Parconier/OTUS/Construction System/Enclosures - v0.2/Actuators/Motor - v0.1/motor_closure1p_color_x2_v0.1.stl

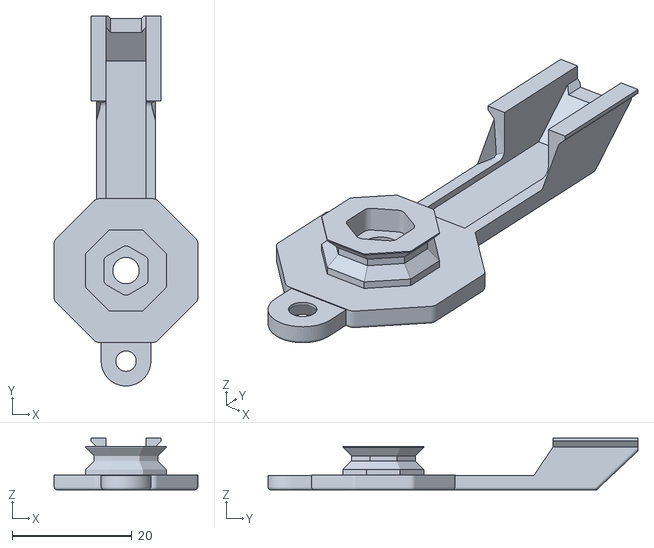
[picture p18: CAD file, 2019-10-22]
Construction System/Enclosures - v0.2/Actuators/Motor - v0.1/motor_closure1p_color_x2_v0.1.stl
24.0 x 61.8 x 8.65
