Parconier/OTUS/Construction System/Enclosures - v0.2/Actuators/Potenciometer - v0.2/pote_knob_neutral_x1_v0.2.stl

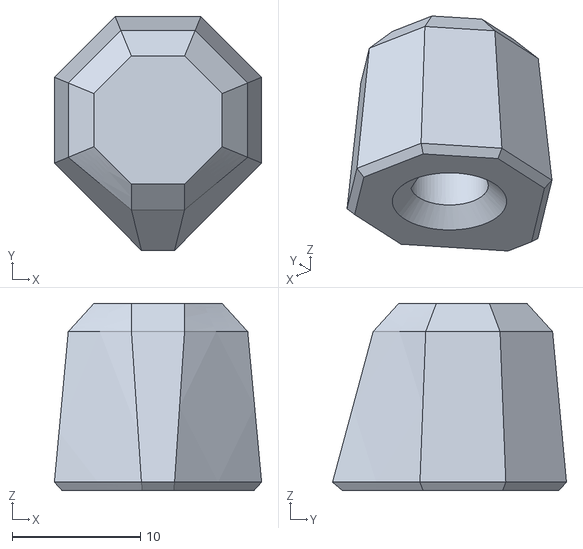
[picture p19: CAD file, 2019-10-22]
Construction System/Enclosures - v0.2/Actuators/Potenciometer - v0.2/pote_knob_neutral_x1_v0.2.stl
16.2 x 18.3 x 14.6
