Parconier/OTUS/Construction System/Enclosures - v0.2/Actuators/Servomotor - v0.1/servo_closure_neutral_x2_v0.1.stl

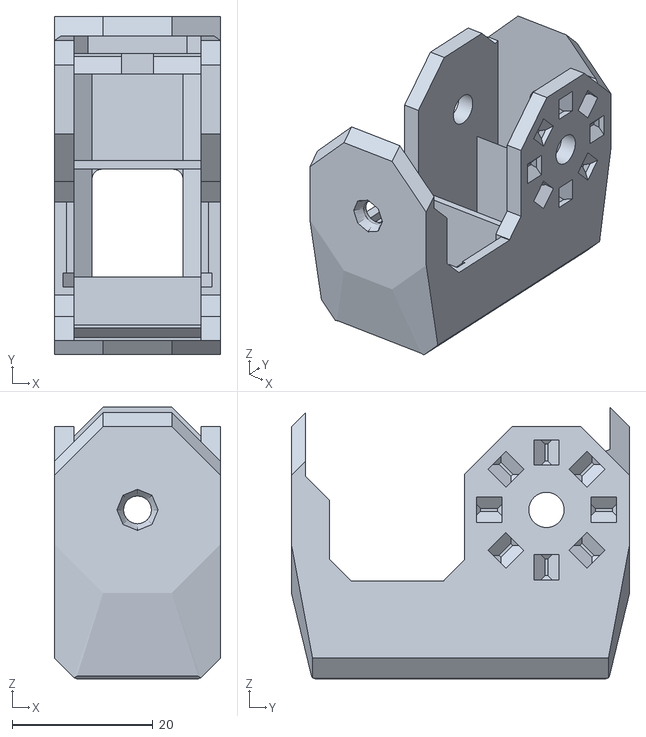
[picture p20: CAD file, 2019-10-22]
Construction System/Enclosures - v0.2/Actuators/Servomotor - v0.1/servo_closure_neutral_x2_v0.1.stl
23.6 x 48.0 x 38.6
