Parconier/OTUS/Construction System/Enclosures - v0.2/Others/Adapter - v0.2/adapter_male_color_x1_v0.2.stl

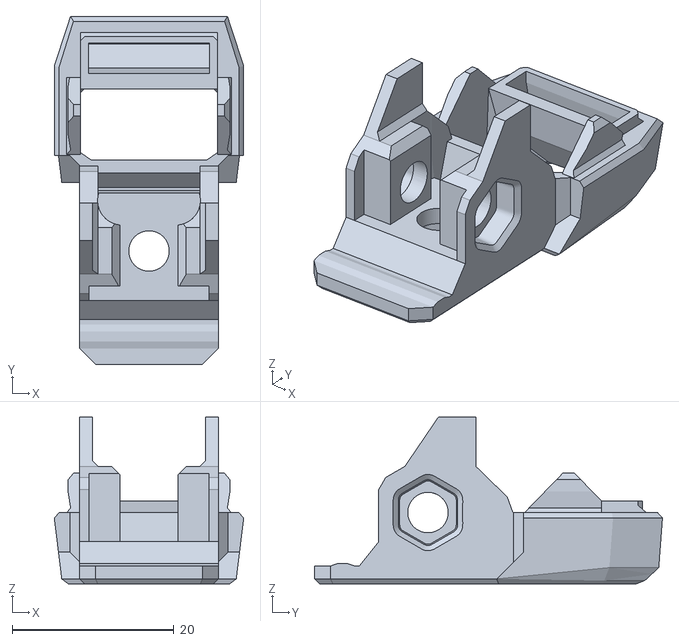
[picture p22: CAD file, 2019-10-22]
Construction System/Enclosures - v0.2/Others/Adapter - v0.2/adapter_male_color_x1_v0.2.stl
23.4 x 43.1 x 20.6
