Parconier/OTUS/Construction System/Enclosures - v0.2/Sensors/Contrast_Sensor - v0.2/contrast_female_color_x2_v0.2.stl

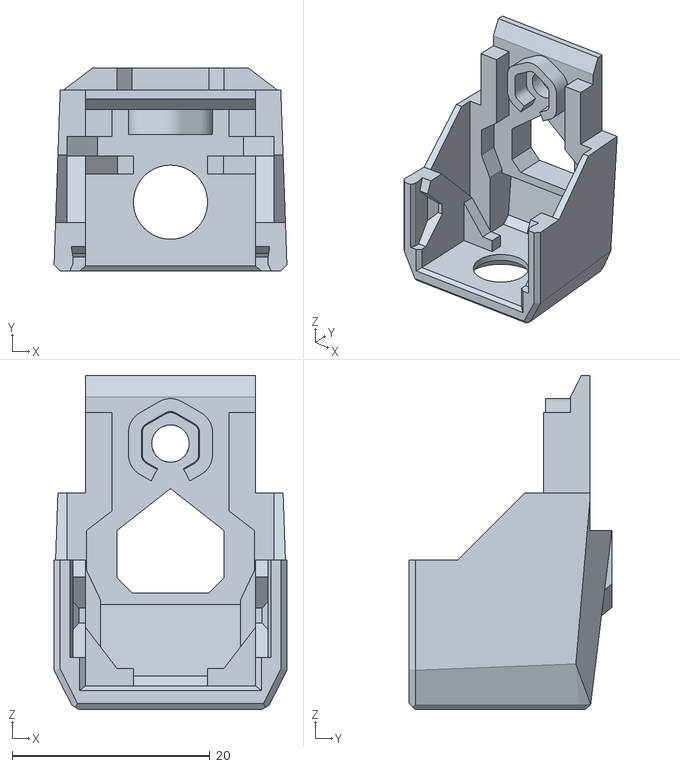
[picture p24: CAD file, 2019-10-22]
Construction System/Enclosures - v0.2/Sensors/Contrast_Sensor - v0.2/contrast_female_color_x2_v0.2.stl
23.6 x 20.5 x 33.8
