Parconier/OTUS/Construction System/Enclosures - v0.2/Sensors/Distance_Sensor - v0.2/distance_male_neutral_x1_v0.2.stl

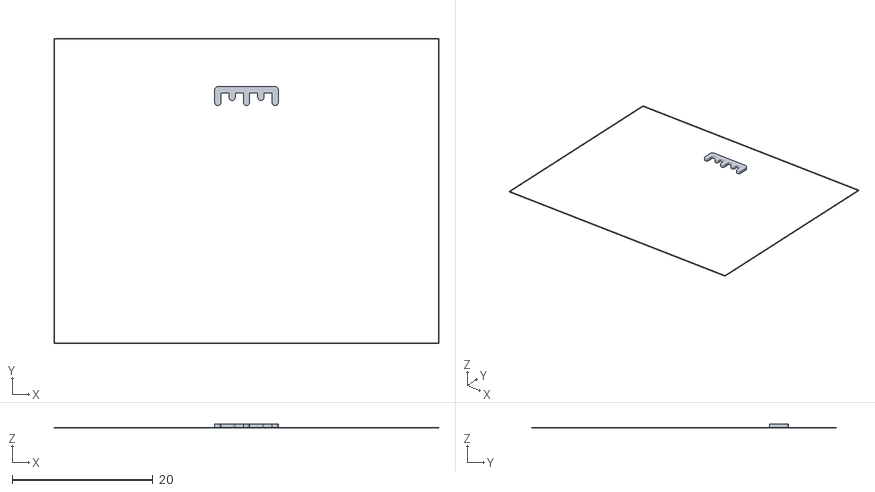
[picture p25: CAD file, 2019-10-22]
Construction System/Enclosures - v0.2/Sensors/Distance_Sensor - v0.2/distance_male_neutral_x1_v0.2.stl
54.6 x 43.4 x 0.6
