Parconier/OTUS/Construction System/Enclosures - v0.2/Sensors/LED_Matrix_3x3 - v0.2/LEDM3x3_male_color_x1_v0.2.stl

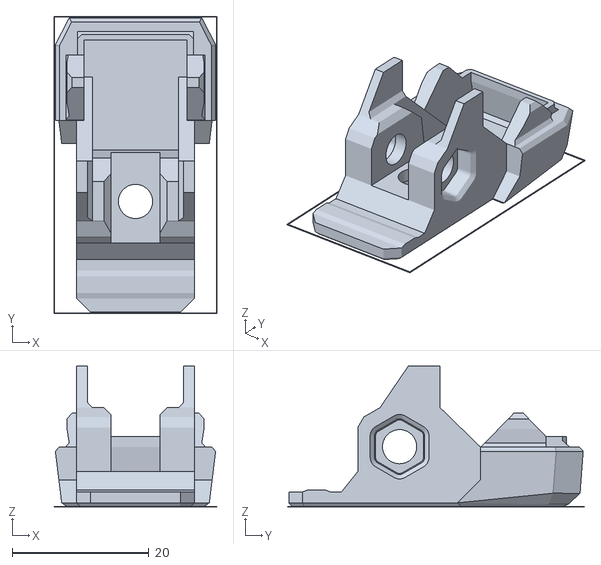
[picture p27: CAD file, 2019-10-22]
Construction System/Enclosures - v0.2/Sensors/LED_Matrix_3x3 - v0.2/LEDM3x3_male_color_x1_v0.2.stl
23.8 x 43.5 x 20.6
