Parconier/OTUS/Construction System/Others - v0.2/Omni_wheel - v0.2/Omni_wheel_color_x1_v0.2.stl

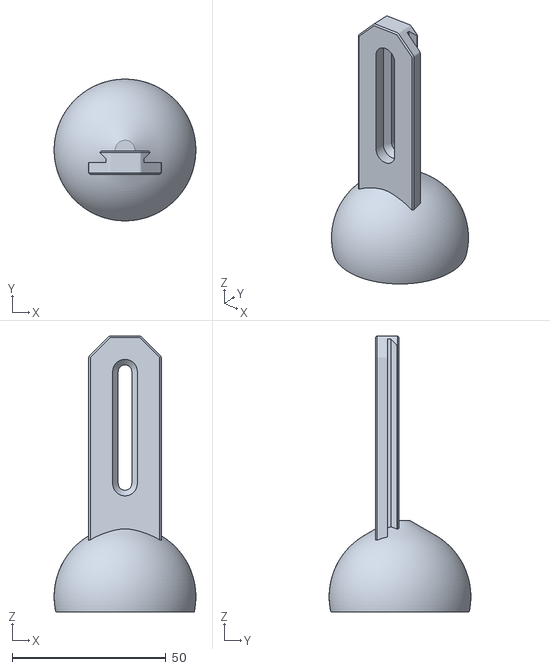
[picture p28: CAD file, 2019-10-22]
Construction System/Others - v0.2/Omni_wheel - v0.2/Omni_wheel_color_x1_v0.2.stl
46.1 x 46.1 x 89.8
