Parconier/OTUS/Construction System/Patterns - v0.2/90degrees_color_x4 - v0.2.stl

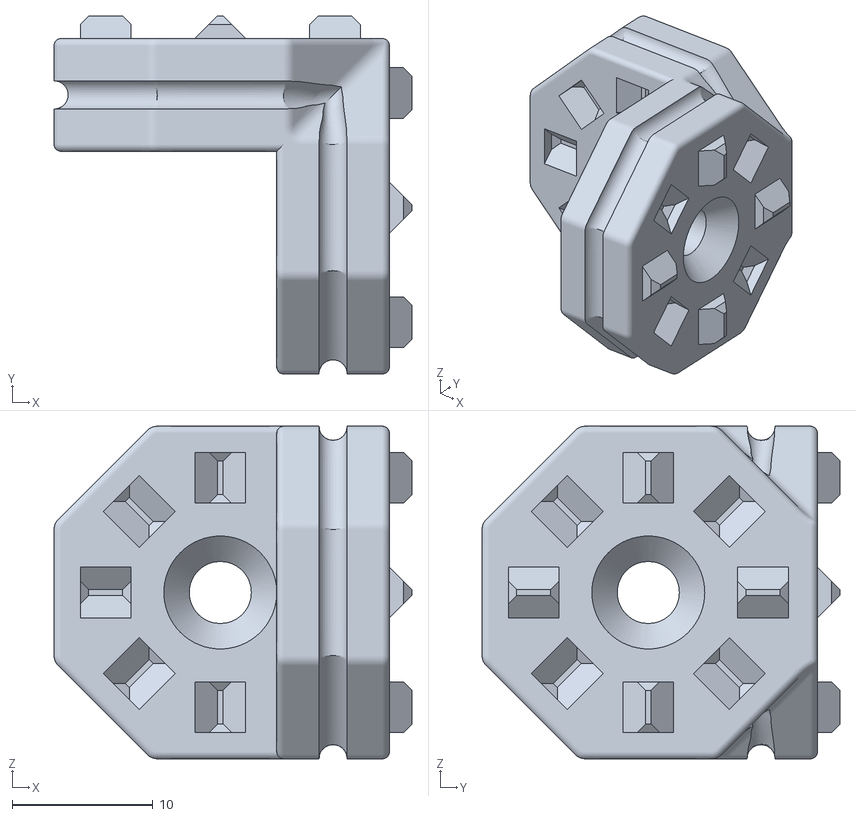
[picture p29: CAD file, 2019-10-18]
Construction System/Patterns - v0.2/90degrees_color_x4 - v0.2.stl
25.4 x 25.4 x 23.6
