Parconier/OTUS/Construction System/Enclosures - v0.2/Actuators/Motor - v0.1/wheel_color_x2_v0.1.stl

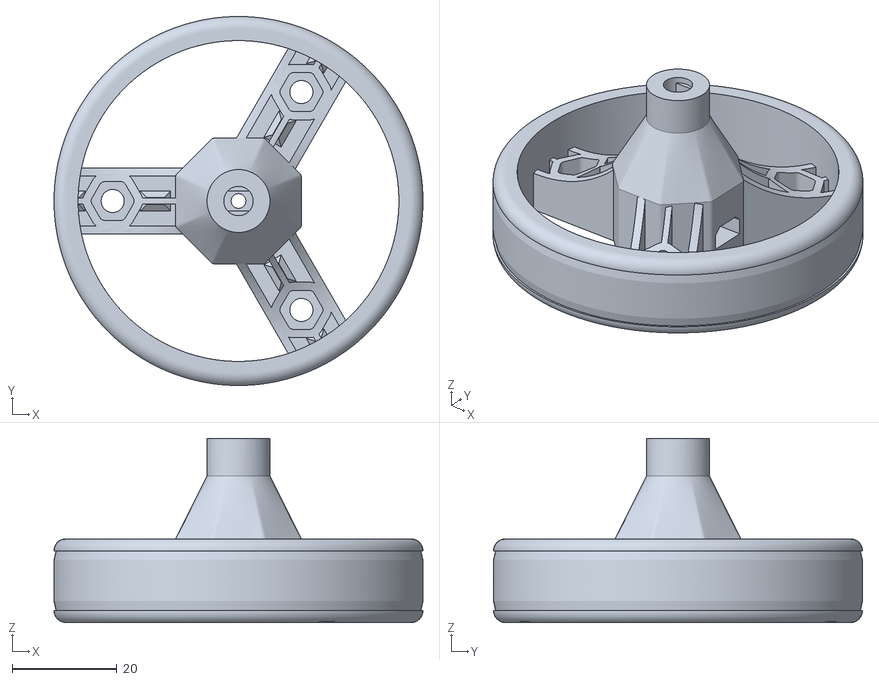
[picture p30: CAD file, 2019-10-22]
Construction System/Enclosures - v0.2/Actuators/Motor - v0.1/wheel_color_x2_v0.1.stl
70.4 x 70.4 x 35.2
