Parconier/OTUS/Construction System/Enclosures - v0.2/Actuators/Potenciometer - v0.2/pote_closure_neutral_x1_v0.2.stl

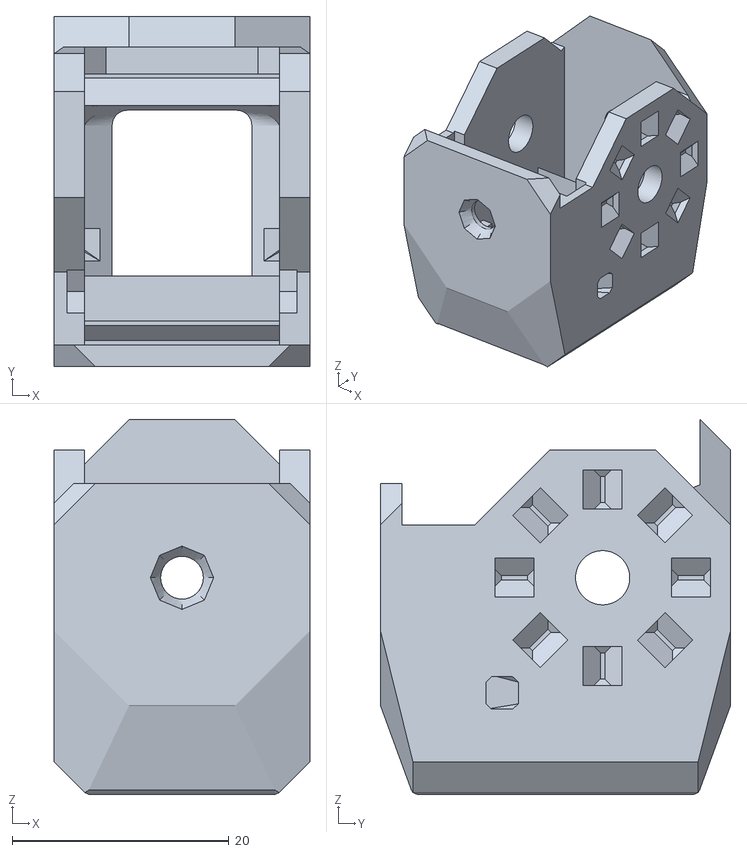
[picture p31: CAD file, 2019-10-22]
Construction System/Enclosures - v0.2/Actuators/Potenciometer - v0.2/pote_closure_neutral_x1_v0.2.stl
23.6 x 32.3 x 34.6
