Parconier/OTUS/Construction System/Enclosures - v0.2/Interface - v0.2/interface_motor_color_x1_v0.2.stl

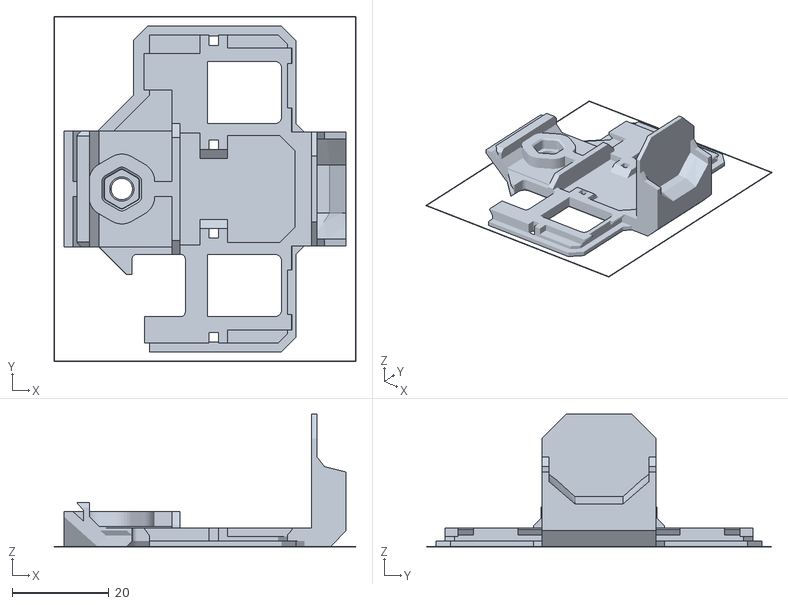
[picture p33: CAD file, 2019-10-22]
Construction System/Enclosures - v0.2/Interface - v0.2/interface_motor_color_x1_v0.2.stl
62.4 x 71.3 x 27.4
