Parconier/OTUS/Construction System/Enclosures - v0.2/Others/Adapter - v0.2/adapter_closure_neutral_x1_v0.2.stl

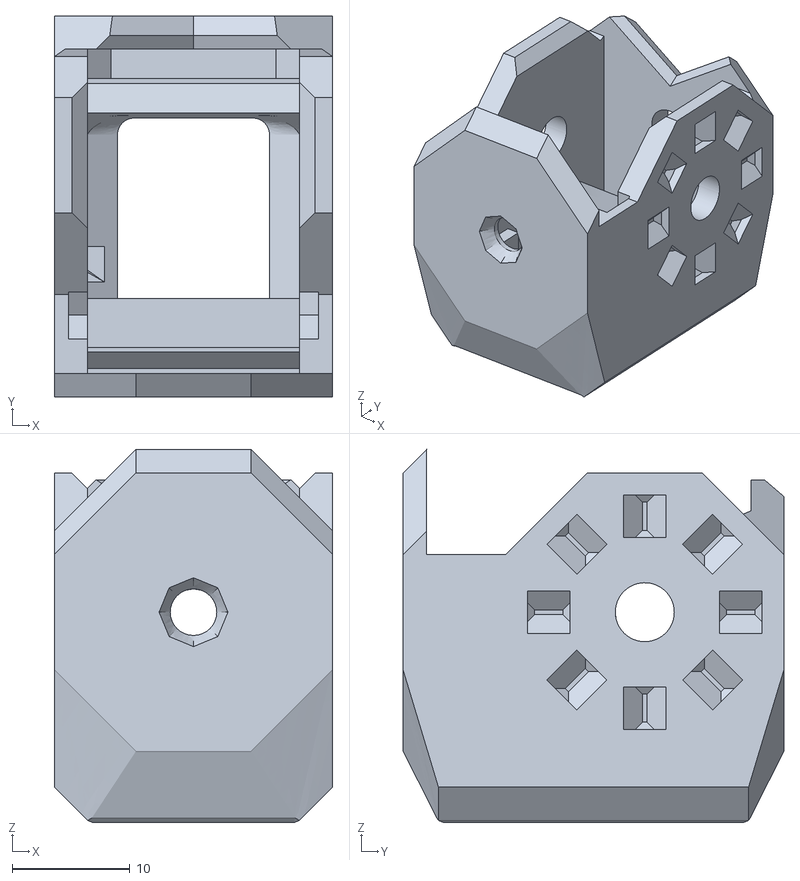
[picture p34: CAD file, 2019-10-22]
Construction System/Enclosures - v0.2/Others/Adapter - v0.2/adapter_closure_neutral_x1_v0.2.stl
23.6 x 32.3 x 31.6
