Parconier/OTUS/Construction System/Enclosures - v0.2/Sensors/Button_Sensor - v0.2/button_button_neutral_x1_v0.2.stl

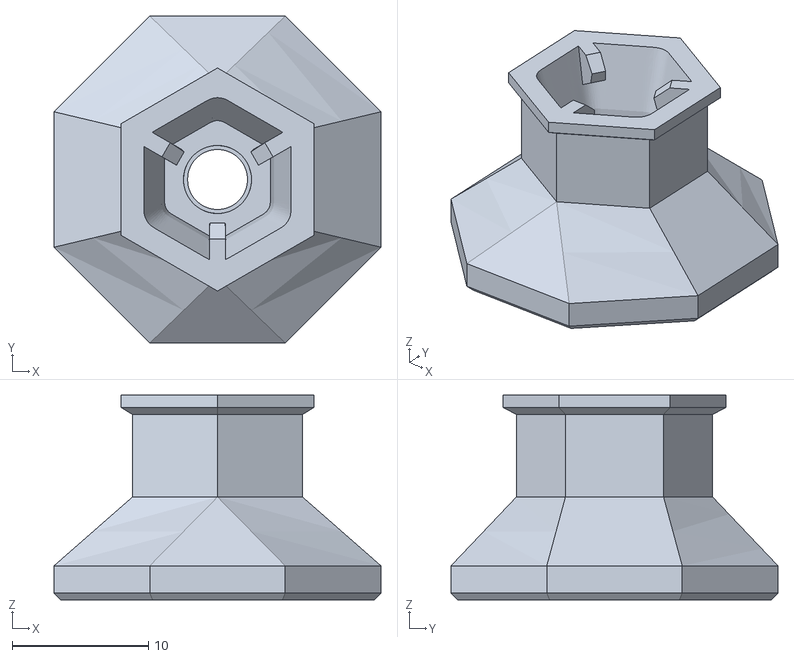
[picture p35: CAD file, 2019-10-22]
Construction System/Enclosures - v0.2/Sensors/Button_Sensor - v0.2/button_button_neutral_x1_v0.2.stl
24.0 x 24.0 x 15.0
