Parconier/OTUS/Construction System/Enclosures - v0.2/Sensors/Contrast_Sensor - v0.2/contrast_male_neutral_x2_v0.2.stl

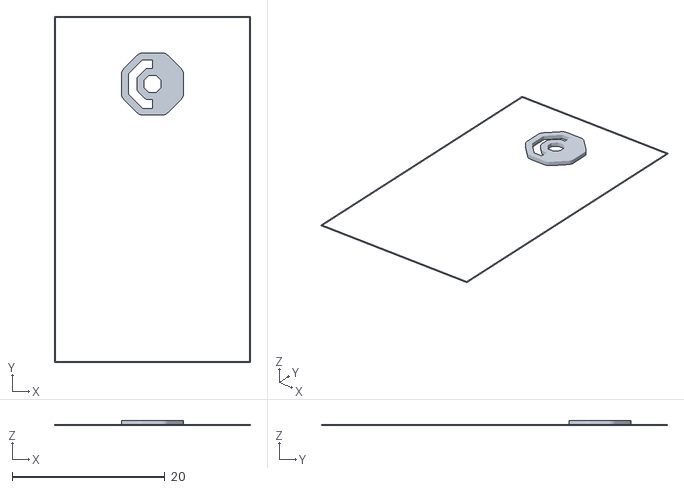
[picture p36: CAD file, 2019-10-22]
Construction System/Enclosures - v0.2/Sensors/Contrast_Sensor - v0.2/contrast_male_neutral_x2_v0.2.stl
25.6 x 45.3 x 0.6
