Parconier/OTUS/Construction System/Enclosures - v0.2/Sensors/LED_Matrix_3x3 - v0.2/LEDM3x3_female_color_x1_v0.2.stl

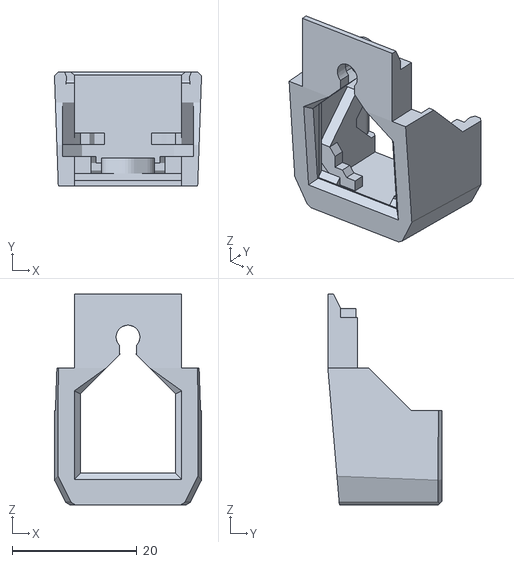
[picture p39: CAD file, 2019-10-22]
Construction System/Enclosures - v0.2/Sensors/LED_Matrix_3x3 - v0.2/LEDM3x3_female_color_x1_v0.2.stl
23.6 x 18.3 x 33.8
