Parconier/OTUS/Construction System/Others - v0.2/Omni_wheel - v0.2/Omni_wheel_v0.2.stp

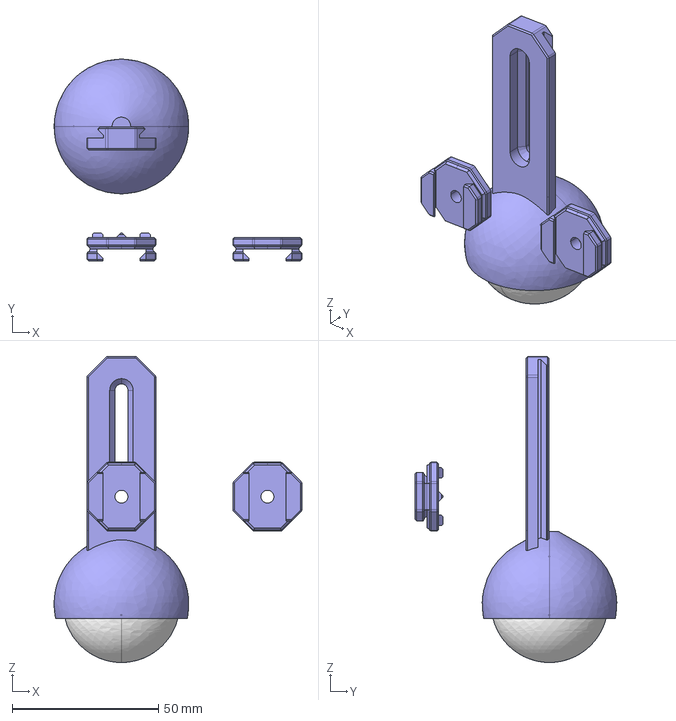
[picture p40: CAD file, 2019-10-22]
Construction System/Others - v0.2/Omni_wheel - v0.2/Omni_wheel_v0.2.stp
84.9 x 69.1 x 104.8 mm
