Parconier/OTUS/Construction System/Patterns - v0.2/Patternx2_color_x6 - v0.2.stl

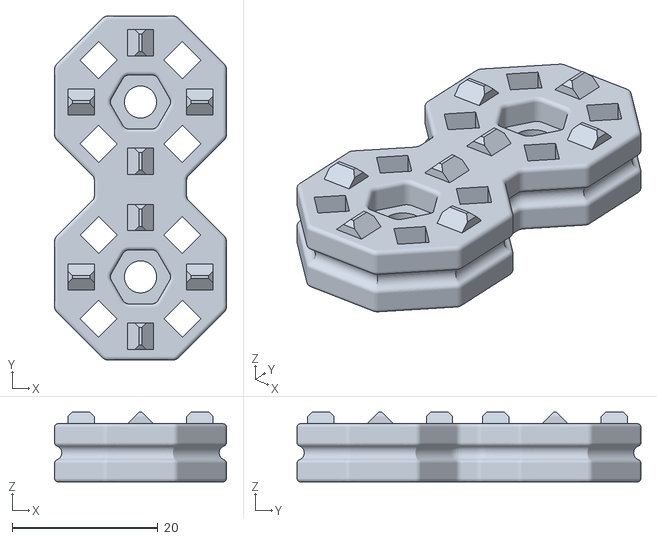
[picture p41: CAD file, 2019-10-18]
Construction System/Patterns - v0.2/Patternx2_color_x6 - v0.2.stl
23.6 x 47.2 x 9.60
