Parconier/OTUS/Construction System/Enclosures - v0.2/Actuators/Motor - v0.1/motor_male_neutral_x2_v0.1.stl

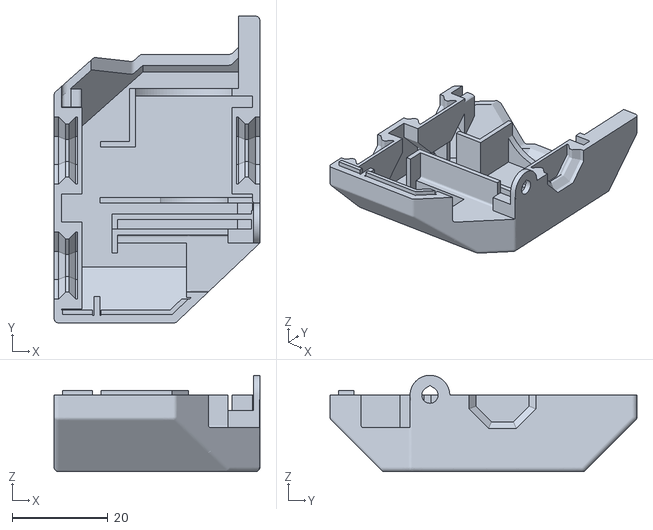
[picture p42: CAD file, 2019-10-22]
Construction System/Enclosures - v0.2/Actuators/Motor - v0.1/motor_male_neutral_x2_v0.1.stl
43.0 x 64.1 x 20.1
