Parconier/OTUS/Construction System/Enclosures - v0.2/Actuators/Servomotor - v0.1/servo_male_color_x2_v0.1.stl

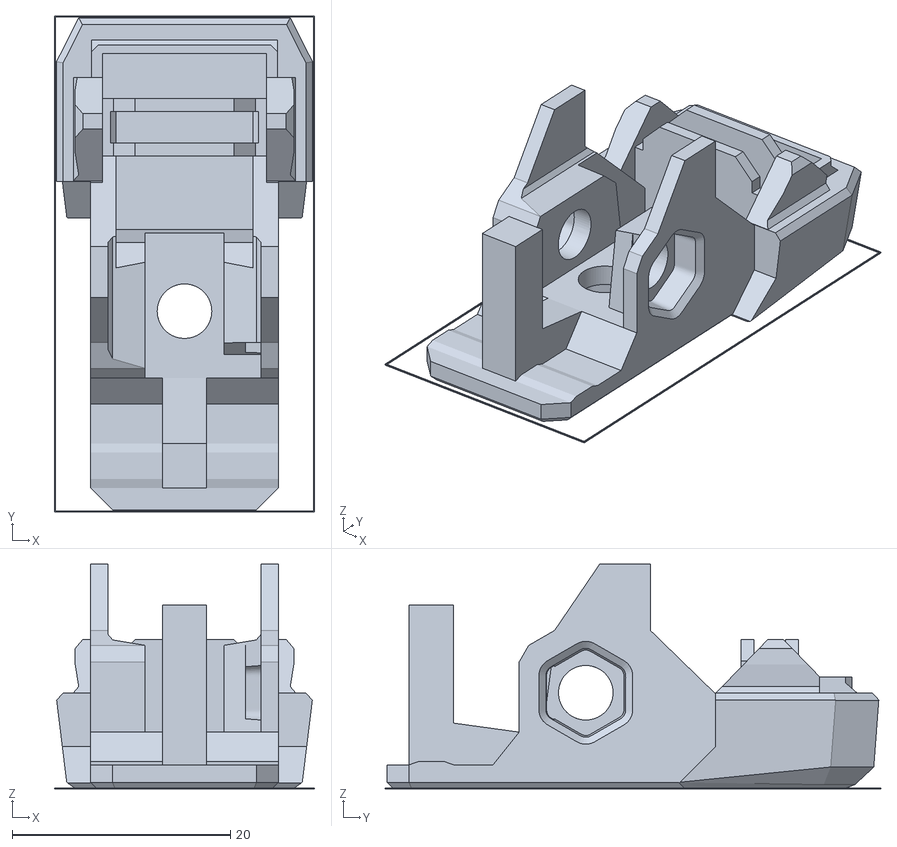
[picture p43: CAD file, 2019-10-22]
Construction System/Enclosures - v0.2/Actuators/Servomotor - v0.1/servo_male_color_x2_v0.1.stl
23.8 x 45.5 x 20.6
