Parconier/OTUS/Construction System/Enclosures - v0.2/Interface - v0.2/interface_sideA_neutral_x1_v0.2.stl

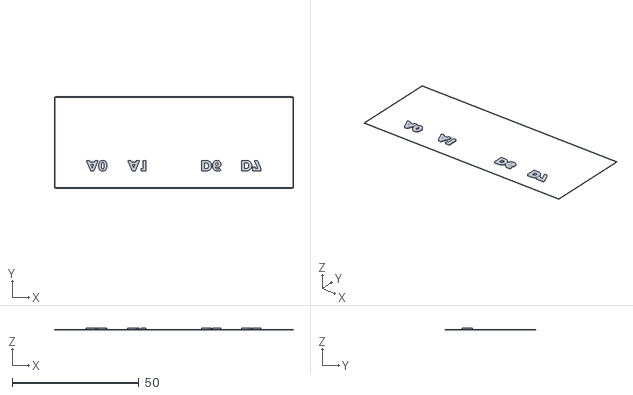
[picture p44: CAD file, 2019-10-22]
Construction System/Enclosures - v0.2/Interface - v0.2/interface_sideA_neutral_x1_v0.2.stl
94.2 x 36.0 x 0.6
