Parconier/OTUS/Construction System/Enclosures - v0.2/Others/Adapter - v0.2/adapter_female_color_x1_v0.2.stl

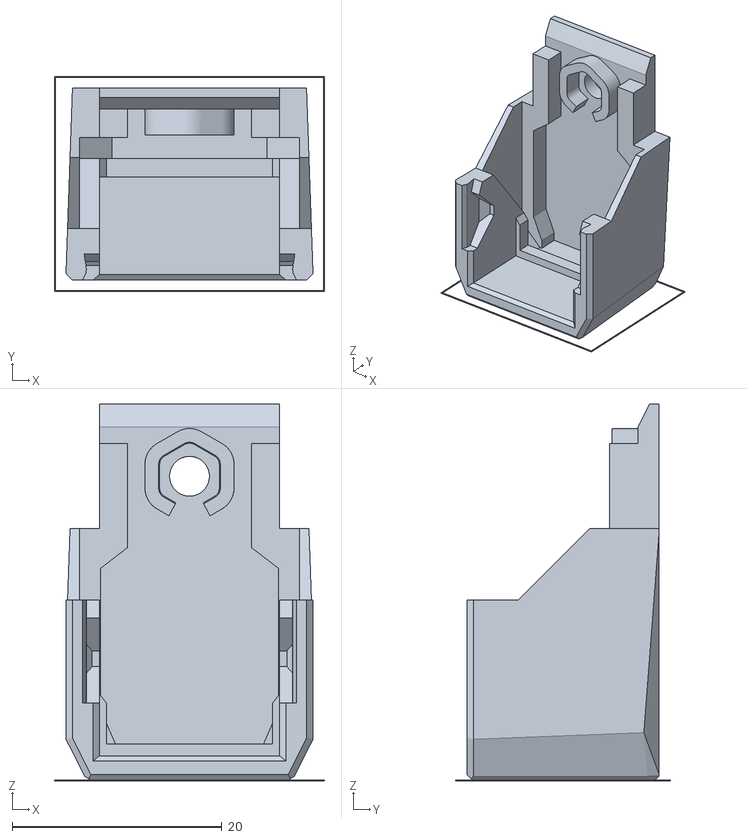
[picture p45: CAD file, 2019-10-22]
Construction System/Enclosures - v0.2/Others/Adapter - v0.2/adapter_female_color_x1_v0.2.stl
25.8 x 20.5 x 35.9
