Parconier/OTUS/Construction System/Enclosures - v0.2/Sensors/Button_Sensor - v0.2/button_female_color_x1_v0.2.stl

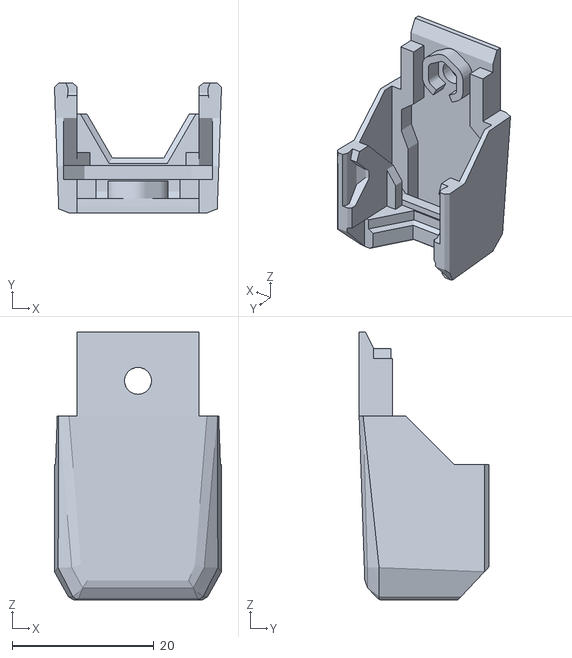
[picture p46: CAD file, 2019-10-22]
Construction System/Enclosures - v0.2/Sensors/Button_Sensor - v0.2/button_female_color_x1_v0.2.stl
23.6 x 18.3 x 37.8
