Parconier/OTUS/Construction System/Enclosures - v0.2/Sensors/Distance_Sensor - v0.2/distance_female_color_x1_v0.2.stl

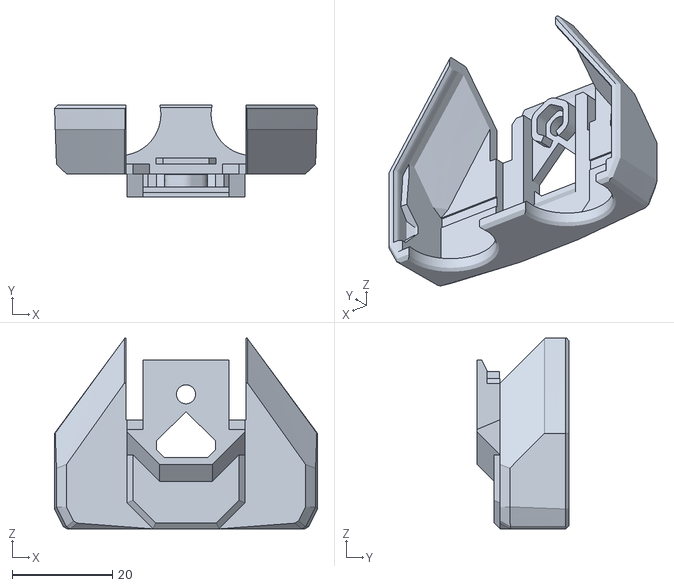
[picture p47: CAD file, 2019-10-22]
Construction System/Enclosures - v0.2/Sensors/Distance_Sensor - v0.2/distance_female_color_x1_v0.2.stl
52.6 x 18.3 x 38.1
