Parconier/OTUS/Construction System/Enclosures - v0.2/Sensors/LED_Matrix_3x3 - v0.2/LEDM3x3_closure_neutral_x1_v0.2.stl

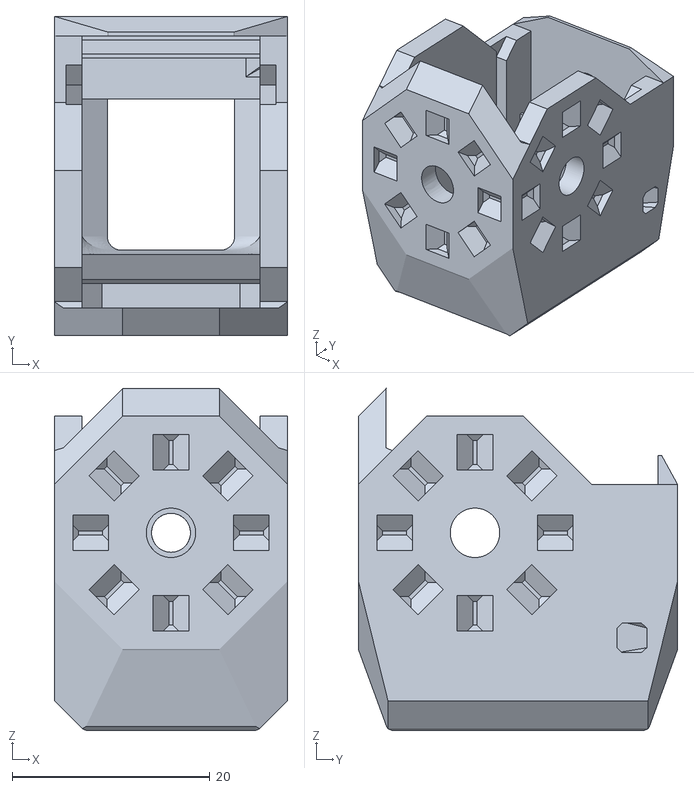
[picture p48: CAD file, 2019-10-22]
Construction System/Enclosures - v0.2/Sensors/LED_Matrix_3x3 - v0.2/LEDM3x3_closure_neutral_x1_v0.2.stl
23.6 x 32.3 x 34.6
