Parconier/OTUS/Construction System/Patterns - v0.2/Patternx3_color_x2 - v0.2.stl

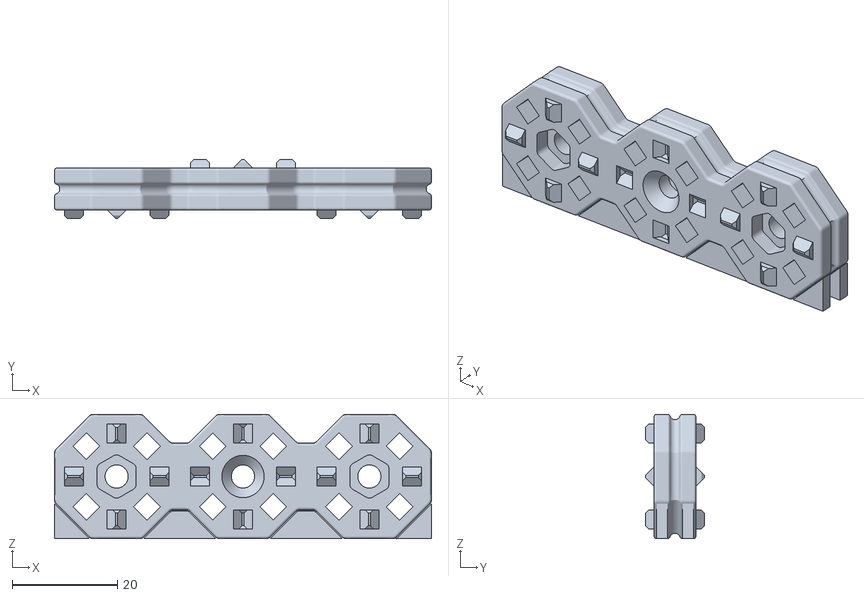
[picture p49: CAD file, 2019-10-18]
Construction System/Patterns - v0.2/Patternx3_color_x2 - v0.2.stl
71.6 x 11.2 x 23.6
