Parconier/OTUS/Construction System/Enclosures - v0.2/Actuators/Potenciometer - v0.2/pote_male_neutral_x1_v0.2.stl

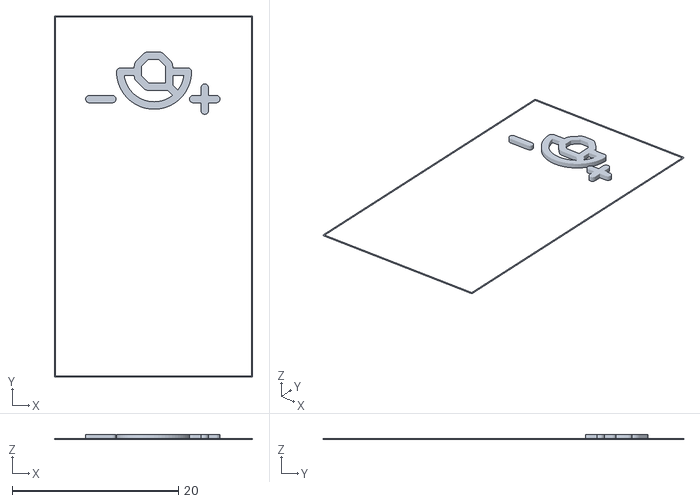
[picture p51: CAD file, 2019-10-22]
Construction System/Enclosures - v0.2/Actuators/Potenciometer - v0.2/pote_male_neutral_x1_v0.2.stl
23.8 x 43.5 x 0.6
