Parconier/OTUS/Construction System/Enclosures - v0.2/Sensors/Button_Sensor - v0.2/button_male_neutral_x1_v0.2.stl

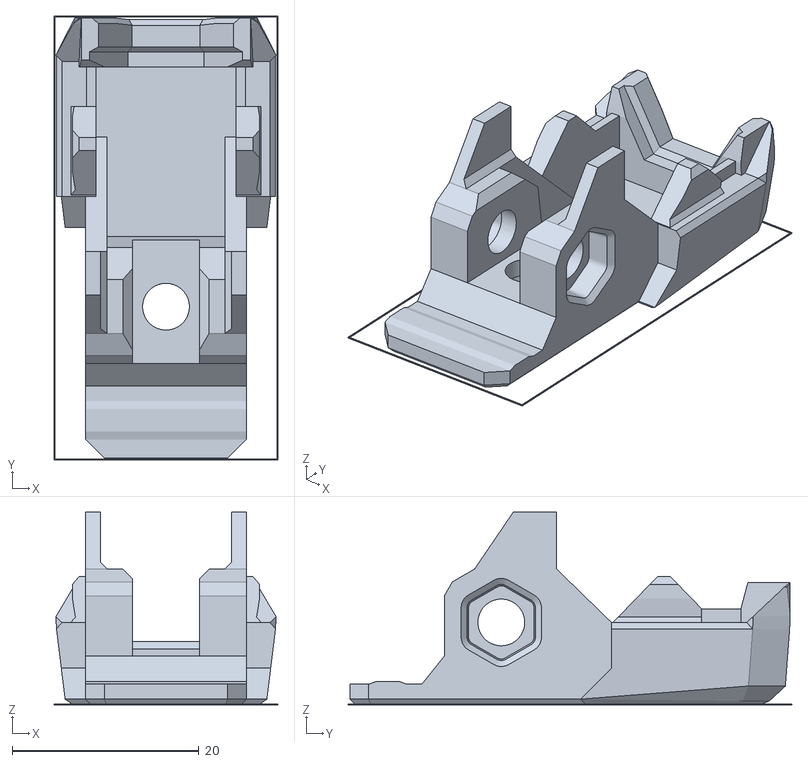
[picture p54: CAD file, 2019-10-22]
Construction System/Enclosures - v0.2/Sensors/Button_Sensor - v0.2/button_male_neutral_x1_v0.2.stl
24.0 x 47.5 x 20.6
