Parconier/OTUS/Construction System/Enclosures - v0.2/Actuators/Motor - v0.1/motor_female_neutral_x2_v0.1.stl

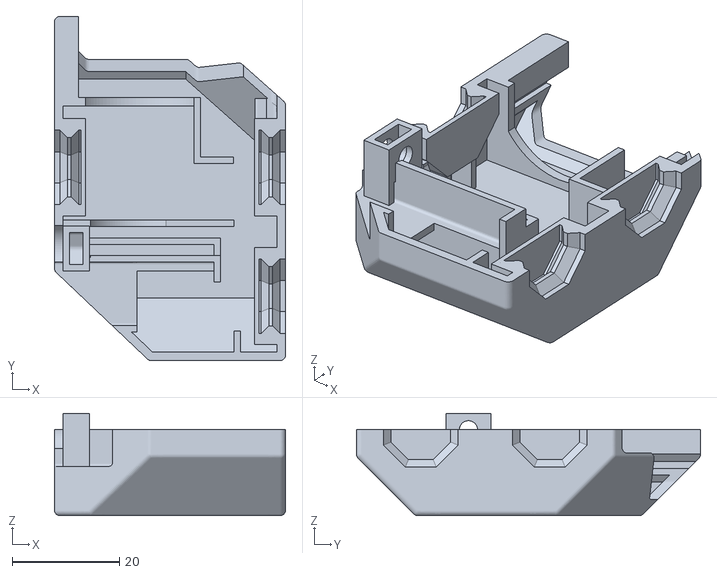
[picture p55: CAD file, 2019-10-22]
Construction System/Enclosures - v0.2/Actuators/Motor - v0.1/motor_female_neutral_x2_v0.1.stl
43.0 x 64.1 x 19.1
