Parconier/OTUS/Construction System/Enclosures - v0.2/Actuators/Servomotor - v0.1/servo_headA_neutral_x2_v0.1.stl

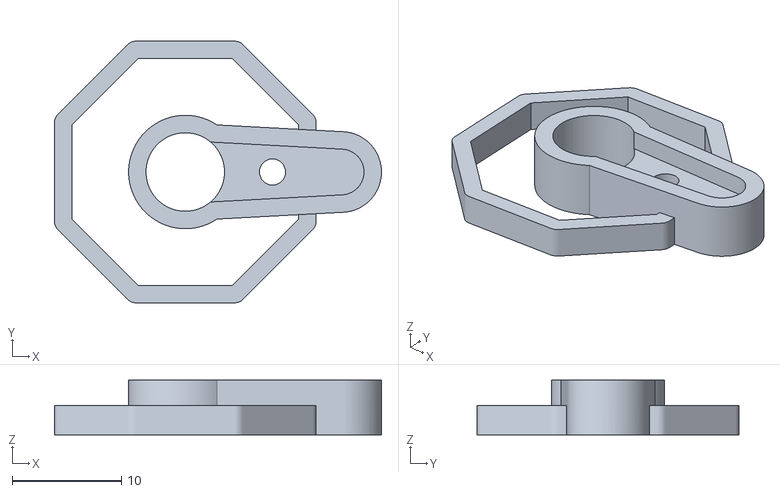
[picture p56: CAD file, 2019-10-22]
Construction System/Enclosures - v0.2/Actuators/Servomotor - v0.1/servo_headA_neutral_x2_v0.1.stl
30.0 x 24.0 x 5.00
