Parconier/OTUS/Construction System/Enclosures - v0.2/Interface - v0.2/interface_connectors_color_x2_v0.2.stl

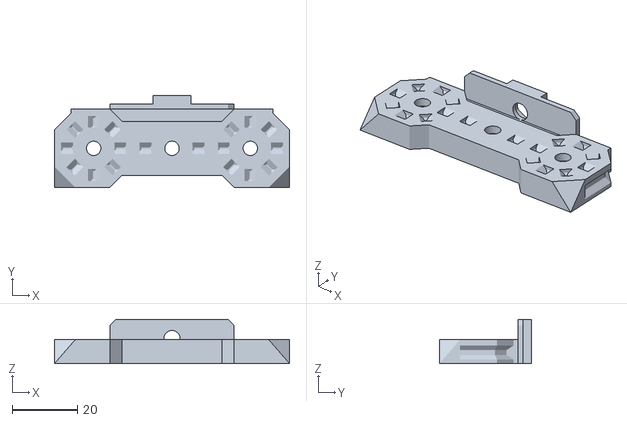
[picture p57: CAD file, 2019-10-22]
Construction System/Enclosures - v0.2/Interface - v0.2/interface_connectors_color_x2_v0.2.stl
72.0 x 28.2 x 13.5
