Parconier/OTUS/Construction System/Enclosures - v0.2/Actuators/Motor - v0.1/motor_axis_color_x2_v0.1.stl

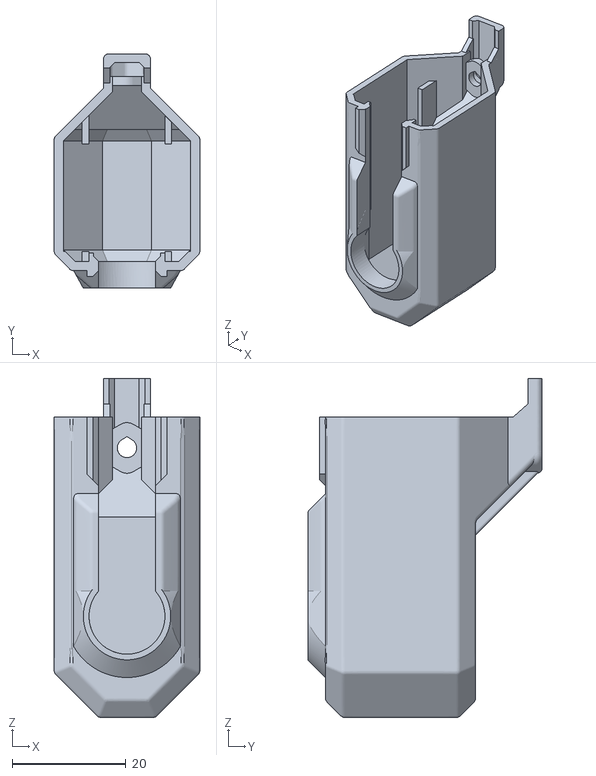
[picture p58: CAD file, 2019-10-22]
Construction System/Enclosures - v0.2/Actuators/Motor - v0.1/motor_axis_color_x2_v0.1.stl
25.6 x 41.2 x 59.6
