Parconier/OTUS/Construction System/Enclosures - v0.2/Interface - v0.2/interface_button_neutral_x1_v0.2.stl

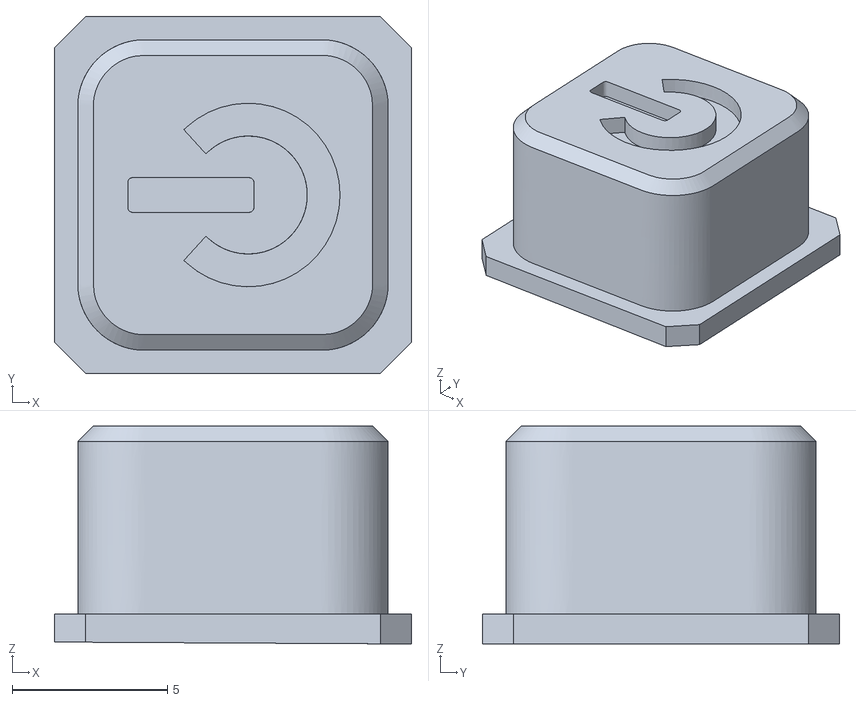
[picture p60: CAD file, 2019-10-22]
Construction System/Enclosures - v0.2/Interface - v0.2/interface_button_neutral_x1_v0.2.stl
11.5 x 11.5 x 7.02
