Parconier/OTUS/Construction System/Enclosures - v0.2/Interface - v0.2/interface_sideB_color_x1_v0.2.stl

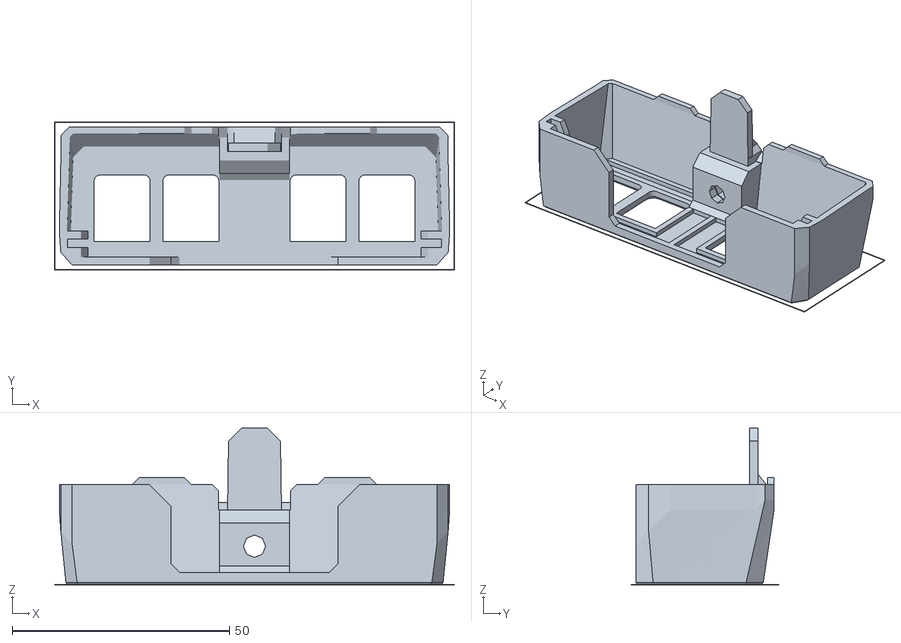
[picture p61: CAD file, 2019-10-22]
Construction System/Enclosures - v0.2/Interface - v0.2/interface_sideB_color_x1_v0.2.stl
92.2 x 34.0 x 36.1
