Parconier/OTUS/Construction System/Enclosures - v0.2/Interface - v0.2/interface_sideB_neutral_x1_v0.2.stl

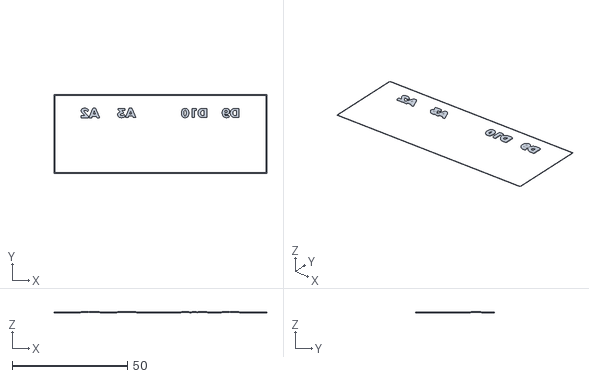
[picture p62: CAD file, 2019-10-22]
Construction System/Enclosures - v0.2/Interface - v0.2/interface_sideB_neutral_x1_v0.2.stl
92.2 x 34.0 x 0.6
